mathompl/AquaLed/src/Nextion.ino

/*
   AQUALED Nextion support functions (c) T. Formanowski 2016-2017
   https://github.com/mathompl/AquaLed
 */



#include <Arduino.h>
#include <MemoryFree.h>
#include "Nextion.h"
#ifndef NO_NEXTION
// init nextion lcd
static void nexInit(void)
{
        NEXTION_BEGIN (9600);
        sendNextionEOL ();
        setPage(PAGE_HOME);
        setInt (NX_FIELD_BAUDS, NX_FIELD_EMPTY, (long)NEXTION_BAUD_RATE);
        NEXTION_FLUSH ();
        delay (50);
        NEXTION_BEGIN ((long)NEXTION_BAUD_RATE);
        setInt (NX_FIELD_BKCMD, NX_FIELD_EMPTY, (long)0);
        setPage (PAGE_HOME);
        toggleButtons ();
        refreshPWMNames ();
        forceRefresh = true;
        NEXTION_FLUSH ();
}

static void refreshPWMNames ()
{
        // init names
        for (byte i = 0; i < PWMS; i++)
        {
                setText (PAGE_HOME, NX_FIELD_LD1+i, (char*)pgm_read_word(&(nx_pwm_names[i])));
                delay(1);
                setText (PAGE_PWM_LIST, NX_FIELD_BLD1+i, (char*)pgm_read_word(&(nx_pwm_names[i])));
                delay(1);
        }
}

// main touch listener
static void nxTouch()
{
        while (NEXTION_AVAIL ()> 0)
        {

                char c = NEXTION_READ ();
                if (c == NEX_RET_EVENT_TOUCH_HEAD)
                {
                        memset(__touch_buffer, 0, sizeof (__touch_buffer));
                        __touch_event = true;
                }
                if (__touch_event)
                {
                        __touch_buffer[__touch_buffer_ix] = c;
                        __touch_buffer_ix++;
                }

                if (__touch_buffer_ix == 7)
                {
                        if (memcmp( __touch_buffer+3, nextionEol, 3)) handlePage ( __touch_buffer[1], __touch_buffer[2]);
                        __touch_buffer_ix = 0;
                        __touch_event = false;
                        return;
                }

        }
}
static void handlePage (byte pid, byte cid)
{
        lastTouch = currentMillis;
        switch (pid)
        {
        case PAGE_HOME:
                handleHomePage (cid);
                break;

        case PAGE_CONFIG:
                handleConfigPage (cid);
                break;

        case PAGE_SETTIME:
                handleSetTimePage (cid);
                break;

        case PAGE_SETTINGS:
                handleSettingsPage (cid);
                break;

        case PAGE_PWM:
                handlePWMPage (cid);
                break;

        case PAGE_TEST:
                handleTestPage (cid);
                break;

        case PAGE_SCREENSAVER:
                handleScreenSaver (cid);
                break;

        case PAGE_THERMO:
                handleThermoPage (cid);
                break;

        case PAGE_SCHEDULE:
                handleSchedulePage (cid);
                break;

        case PAGE_PWM_LIST:
                handlePWMListPage (cid);
                break;

        case PAGE_ERROR:
                handleScreenSaver (cid);
                break;

        case PAGE_PWMSTATUS:
                handlePWMStatus (cid);
                break;

        default:
                break;
        }
        lastTouch = currentMillis;
}

static void handleScreenSaver (byte cid)
{
        forceRefresh = true;
        setPage (PAGE_HOME);
        lastTouch = currentMillis;
        toggleButtons();
        refreshPWMNames ();
        refreshHomePage ();
}

static boolean setThermo (byte page, byte field, byte i)
{
        if (!getNumber(page, field, &t)) return false;
        for (byte k = 0; k < 8; k++)
                settings.sensors[i][k] = sensorsList[t].address[k];
        return true;
}

static void handleThermoPage (byte cid)
{
        boolean status = false;
        switch (cid)
        {
        // save
        case THERMOPAGE_BUTTON_SAVE:
                setPage (PAGE_SAVING);
                if (!setThermo (PAGE_THERMO, NX_FIELD_N0, LED_TEMPERATURE_FAN)) break;
                if (!setThermo (PAGE_THERMO, NX_FIELD_N1, SUMP_TEMPERATURE_FAN)) break;
                if (!setThermo (PAGE_THERMO, NX_FIELD_N2, WATER_TEMPERATURE_FAN)) break;
                writeEEPROMSettings ();
                lastTouch = currentMillis;
                setPage (PAGE_CONFIG);
                status = true;
                break;

        //cancel
        case THERMOPAGE_BUTTON_CANCEL:
                lastTouch = currentMillis;
                setPage (PAGE_CONFIG);
                status = true;
                break;

        default:
                break;
        }
        if (!status) setPage (PAGE_THERMO);
}

static void handleSchedulePage (byte cid)
{
        switch (cid)
        {
        //cancel
        case SCHEDULEPAGE_BUTTON_CLOSE:
                lastTouch = currentMillis;
                setPage (PAGE_CONFIG);
                break;

        default:
                break;
        }
}

static boolean handleTestSlider (int field, byte i)
{
        if (!getNumber(field, &t)) return false;
        pwmRuntime[i].valueCurrent = mapRound ((long)t, 0, 100, 0, PWM_I2C_MAX);
        pwmRuntime[i].testMode = true;
        return true;
}

static void handleTestPage (byte cid)
{
        switch (cid)
        {
        // pwms
        case TESTPAGE_SLIDER_PWM_1:
                handleTestSlider (NX_FIELD_N0, 0);
                break;
        case TESTPAGE_SLIDER_PWM_2:
                handleTestSlider (NX_FIELD_N1, 1);
                break;
        case TESTPAGE_SLIDER_PWM_3:
                handleTestSlider (NX_FIELD_N2, 2);
                break;
        case TESTPAGE_SLIDER_PWM_4:
                handleTestSlider (NX_FIELD_N3, 3);
                break;
        case TESTPAGE_SLIDER_PWM_5:
                handleTestSlider (NX_FIELD_N4, 4);
                break;
        case TESTPAGE_SLIDER_PWM_6:
                handleTestSlider (NX_FIELD_N5, 5);
                break;
        case TESTPAGE_SLIDER_PWM_7:
                handleTestSlider (NX_FIELD_N6, 6);
                break;
        case TESTPAGE_SLIDER_PWM_8:
                handleTestSlider (NX_FIELD_N7, 7);
                break;

        // close
        case TESTPAGE_BUTTON_CLOSE:
                lastTouch = currentMillis;
                forcePWMRecovery (true);
                for (byte i = 0; i < PWMS; i++)
                {
                        //pwmRuntime[i].valueTest = 0;
                        pwmRuntime[i].testMode = false;
                }
                setPage (PAGE_CONFIG);
                break;

        default:
                break;
        }
}

static void handlePWMPage (byte cid)
{
        int i;
        byte lastPin;
        byte lastI2C;
        boolean status = false;
        switch (cid)
        {
        // save
        case PWMPAGE_BUTTON_SAVE:
                setPage (PAGE_SAVING);
                if (!getNumber(PAGE_PWM, NX_FIELD_N9, &i)) break;
                if (i < 1 || i > PWMS) break;
                lastPin = pwmSettings[i - 1].pin;
                lastI2C = pwmSettings[i - 1].isI2C;

                if (!getNumber(PAGE_PWM, NX_FIELD_C0, &pwmSettings[i - 1].enabled )) break;
                if (!getNumber(PAGE_PWM, NX_FIELD_C1, &pwmSettings[i - 1].isNightLight)) break;
                if (!getNumber(PAGE_PWM, NX_FIELD_C2, &pwmSettings[i - 1].isProg)) break;
                if (!getNumber(PAGE_PWM, NX_FIELD_N0, &pwmSettings[i - 1].onHour)) break;
                if (!getNumber(PAGE_PWM, NX_FIELD_N1, &pwmSettings[i - 1].onMinute)) break;
                if (!getNumber(PAGE_PWM, NX_FIELD_N2, &pwmSettings[i - 1].offHour)) break;
                if (!getNumber(PAGE_PWM, NX_FIELD_N3, &pwmSettings[i - 1].offMinute)) break;
                if (!getNumber(PAGE_PWM, NX_FIELD_N4, &pwmSettings[i - 1].sunriseLenght)) break;
                if (!getNumber(PAGE_PWM, NX_FIELD_N5, &pwmSettings[i - 1].sunsetLenght)) break;
                if (!getNumber(PAGE_PWM, NX_FIELD_N6, &pwmSettings[i - 1].valueNight)) break;
                if (!getNumber(PAGE_PWM, NX_FIELD_N7, &pwmSettings[i - 1].valueDay)) break;
                if (!getNumber(PAGE_PWM, NX_FIELD_N8, &pwmSettings[i - 1].valueProg)) return;
                if (!getNumber(PAGE_PWM, NX_FIELD_N10, &pwmSettings[i - 1].pin)) break;
                if (!getNumber(PAGE_PWM, NX_FIELD_N11, &pwmSettings[i - 1].watts)) break;
                if (!getNumber(PAGE_PWM, NX_FIELD_C3, &pwmSettings[i - 1].isI2C)) break;
                if (!getNumber(PAGE_PWM, NX_FIELD_C4, &pwmSettings[i - 1].invertPwm)) break;
                if (!getNumber(PAGE_PWM, NX_FIELD_C5, &pwmSettings[i - 1].useLunarPhase)) break;

                if (lastPin != pwmSettings[i - 1].pin || lastI2C != pwmSettings[i - 1].isI2C) initPWM ( i-1 );

                //pwmSettings[i - 1].valueNight = mapRound ((byte)pwmSettings[i - 1].valueNight, 0, 255, 0, PWM_I2C_MAX);
                pwmSettings[i - 1].valueProg = mapRound (pwmSettings[i - 1].valueProg, 0, 100, 0, PWM_I2C_MAX);
                pwmSettings[i - 1].valueDay = mapRound (pwmSettings[i - 1].valueDay, 0, 100, 0, PWM_I2C_MAX);
                lastTouch = currentMillis;
                writeEEPROMPWMConfig (i - 1);
                updateChannelTimes (i-1);
                setPage (PAGE_PWM_LIST);
                status = true;
                break;

        //  cancel
        case PWMPAGE_BUTTON_CANCEL:
                lastTouch = currentMillis;
                setPage (PAGE_PWM_LIST);
                status = true;
                break;

        default:
                status = true;
                break;
        }
        if (!status) setPage (PAGE_PWM_LIST);
}

static void handleSettingsPage (byte cid)
{
        boolean status = false;
        switch (cid)
        {
        // save
        case SETTINGSPAGE_BUTTON_SAVE:
                setPage (PAGE_SAVING);
                if (!getNumber(PAGE_SETTINGS,NX_FIELD_N0, &settings.maxTemperatures[LED_TEMPERATURE_FAN] )) break;
                if (!getNumber(PAGE_SETTINGS,NX_FIELD_N1, &settings.maxTemperatures[SUMP_TEMPERATURE_FAN])) break;
                if (!getNumber(PAGE_SETTINGS,NX_FIELD_N2, &settings.maxTemperatures[WATER_TEMPERATURE_FAN])) break;
                if (!getNumber(PAGE_SETTINGS,NX_FIELD_N3, &settings.pwmDimmingTime)) break;
                if (!getNumber(PAGE_SETTINGS,NX_FIELD_N4, &settings.screenSaverTime)) break;
                if (!getNumber(PAGE_SETTINGS,NX_FIELD_C0, &settings.softDimming)) break;
                writeEEPROMSettings ();
                lastTouch = currentMillis;
                setPage (PAGE_CONFIG);
                status = true;
                break;

        // cancel
        case SETTINGSPAGE_BUTTON_CANCEL:
                lastTouch = currentMillis;
                setPage (PAGE_CONFIG);
                status = true;
                break;

        default:
                break;
        }
        if (!status) setPage (PAGE_SETTINGS);
}

static void handleSetTimePage (byte cid)
{
        int setHour, setMinute, setYear, setMonth, setDay;
        boolean status = false;
        switch (cid)
        {
        // save
        case TIMEPAGE_BUTTON_SAVE:
                setPage (PAGE_SAVING);
                if (!getNumber(PAGE_SETTIME, NX_FIELD_N0, &setHour)) break;
                if (!getNumber(PAGE_SETTIME, NX_FIELD_N1, &setMinute)) break;
                if (!getNumber(PAGE_SETTIME, NX_FIELD_N2, &setDay)) break;
                if (!getNumber(PAGE_SETTIME, NX_FIELD_N3, &setMonth)) break;
                if (!getNumber(PAGE_SETTIME, NX_FIELD_N4, &setYear)) break;
                if (!getNumber(PAGE_SETTIME, NX_FIELD_C0, &settings.dst)) break;
                RTC.adjust(DateTime(setYear, setMonth, setDay, setHour, setMinute,0));
                readTimes ();
                adjustDST ();
                writeEEPROMSettings ();
                lastTouch = currentMillis;
                setPage (PAGE_CONFIG);
                lastTouch = currentMillis;
                forcePWMRecovery (false);
                status = true;
                break;

        // cancel
        case TIMEPAGE_BUTTON_CANCEL:
                lastTouch = currentMillis;
                setPage (PAGE_CONFIG);
                lastTouch = currentMillis;
                status = true;
                break;

        default:
                status = true;
                break;
        }
        if (!status) setPage (PAGE_SETTIME);
}

static void drawSchedule ()
{
        int startL;
        int min_start;
        int min_stop;
        int stopL;
        int stopM;
        int min_sunrise;
        int min_sunrise_left;
        int min_sunset;
        int min_sunset_left;
        boolean midnight = false;

        for (byte i = 0; i < PWMS; i++)
        {
                min_start = (int)pwmSettings[i].onHour * (int)60 + (int)pwmSettings[i].onMinute;
                min_stop = (int)pwmSettings[i].offHour * (int)60 + (int)pwmSettings[i].offMinute;

                // background
                if (pwmSettings[i].isNightLight == 1)
                        fillRect (offset * i + startx, starty, width, height, COLOR_DARKBLUE);
                else
                        fillRect (offset * i + startx, starty, width, height, COLOR_RED);

                // off
                if (pwmSettings[i].enabled == 0) continue;

                // light
                if (min_stop < min_start) midnight = true;
                else midnight = false;

                if (!midnight)
                {
                        startL = map (min_start, 0, min_hour, starty, starty + height);
                        stopL = map (min_stop, 0, min_hour, starty, starty + height ) - startL;
                        fillRect (offset * i + startx, startL, width, stopL, COLOR_GREEN);
                }
                else
                {
                        startL = map (min_start, 0, min_hour, starty, starty + height);
                        stopL = map (min_stop, 0, min_hour, starty, starty + height ) - 30;
                        stopM =  map (min_hour, 0, min_hour, starty, starty + height ) - startL;
                        // start to midnight
                        fillRect (offset * i + startx, startL, width, stopM, COLOR_GREEN);
                        // midnight to end
                        fillRect (offset * i + startx, starty, width, stopL, COLOR_GREEN);
                }
                // sunrise
                min_sunrise  = min_start + (int)pwmSettings[i].sunriseLenght;
                if (min_sunrise > min_hour) midnight = true; else midnight = false;

                if (!midnight)
                {
                        startL = map (min_start, 0, min_hour, starty, starty + height);
                        stopL = map (min_sunrise, 0, min_hour, starty, starty + height ) - startL;
                        fillRect (offset * i + startx, startL, width, stopL, COLOR_BLUE);
                }
                else
                {
                        startL = map (min_start, 0, min_hour, starty, starty + height);
                        stopM =  map (min_hour, 0, min_hour, starty, starty + height ) - startL;
                        min_sunrise_left = min_sunrise - min_hour;
                        stopL = map (min_sunrise_left, 0, min_hour, starty, starty + height ) - starty;
                        // start to midnight
                        fillRect (offset * i + startx, startL, width, stopM, COLOR_BLUE);
                        // midnight to end
                        fillRect (offset * i + startx, starty, width, stopL, COLOR_BLUE);
                }
                // sunset
                min_sunset  = min_stop - (int)pwmSettings[i].sunsetLenght;
                if (min_sunset < 0) midnight = true; else midnight = false;
                if (!midnight)
                {
                        startL = map (min_sunset, 0, min_hour, starty, starty + height);
                        stopL = map (min_stop, 0, min_hour, starty, starty + height ) - startL;
                        fillRect (offset * i + startx, startL, width, stopL, COLOR_BLUE);
                }
                else
                {
                        min_sunset_left = min_hour + min_sunset;
                        stopL  = map (min_stop, 0, min_hour, starty, starty + height ) - starty;
                        startL = map (min_sunset_left, 0, min_hour, starty, starty + height);
                        stopM =  map (min_hour, 0, min_hour, starty, starty + height ) - startL;
                        // zero to end
                        fillRect (offset * i + startx, starty, width, stopL, COLOR_BLUE);
                        // rest till midnight
                        fillRect (offset * i + startx, startL, width, stopM, COLOR_BLUE);
                }
        }
        int min_now = map (currHour * 60 + currMinute, 0, min_hour, starty, starty + height);
        fillRect (hour_startx, min_now, hour_stopx, 1, COLOR_YELLOW);
        // siatka dodatkowa
        /*
           for (int i = 0 ; i < 24; i++)
           {
           fillRect (40, 10 * i + starty+1, 180, 1, COLOR_DARKGRAY);

           }*/
}

static void handleConfigPage (byte cid)
{
        byte s;
        byte idxLed, idxSump, idxWater;

        char tempbuff[150] = {0};
        switch (cid)
        {
        // schedule
        case CONFIGPAGE_BUTTON_SCHEDULE:
                setPage (PAGE_SCHEDULE);
                drawSchedule ();
                break;

        // close
        case CONFIGPAGE_BUTTON_CLOSE:
                forceRefresh = true;
                setPage (PAGE_HOME);
                toggleButtons();
                refreshHomePage ();
                break;

        // thermo setup
        case CONFIGPAGE_BUTTON_THERMO:
              #ifndef NO_TEMPERATURE
                setPage (PAGE_THERMO);
                s = discoverOneWireDevices ();
                memset (tempbuff, 0, sizeof (tempbuff));
                setValue (NX_FIELD_VA0, (s-1));
                for (byte i = 0; i < s; i++)
                {
                        sprintf(tempbuff + strlen (tempbuff), "%d. ", i);
                        if (i == 0)
                        {
                                strcpy (tempbuff + strlen (tempbuff), "BRAK ");
                        }
                        else
                        {
                                if (sensorsList[i].detected)
                                        strcpy (tempbuff + strlen (tempbuff), "* ");
                                for (byte k = 0; k < 8; k++)
                                        sprintf (tempbuff + strlen (tempbuff), "%02x ", sensorsList[i].address[k]);
                        }
                        strcpy  (tempbuff + strlen (tempbuff), "\r\n");
                }
                idxLed = listContains (settings.sensors[LED_TEMPERATURE_FAN]);
                idxSump = listContains (settings.sensors[SUMP_TEMPERATURE_FAN]);
                idxWater = listContains (settings.sensors[WATER_TEMPERATURE_FAN]);
                if (idxLed == 255) idxLed = 0;
                if (idxSump == 255) idxSump = 0;
                if (idxWater == 255) idxWater = 0;
                setValue (NX_FIELD_N0, idxLed);
                setValue (NX_FIELD_N1, idxSump);
                setValue (NX_FIELD_N2, idxWater);
                setText (NX_FIELD_T4, (String) tempbuff);
              #endif
                break;

        // test
        case CONFIGPAGE_BUTTON_TEST:
                setPage (PAGE_TEST);
                for (byte i = 0; i < PWMS; i++)
                {
                        setValue (NX_FIELD_N0+i, mapRound (pwmRuntime[i].valueCurrent, 0, PWM_I2C_MAX, 0, 100));
                        setValue (NX_FIELD_C1+i, mapRound (pwmRuntime[i].valueCurrent, 0, PWM_I2C_MAX, 0, 100));
                        //pwmRuntime[i].valueTest = pwmRuntime[i].valueCurrent;
                        pwmRuntime[i].testMode = false;
                }
                break;

        // hour and date setup
        case CONFIGPAGE_BUTTON_TIME:
                setPage (PAGE_SETTIME);
                setValue (NX_FIELD_N0, RTC.now().hour ());
                setValue (NX_FIELD_N1, RTC.now().minute ());
                setValue (NX_FIELD_N2, RTC.now().day ());
                setValue (NX_FIELD_N3, RTC.now().month ());
                setValue (NX_FIELD_N4, RTC.now().year());
                setValue (NX_FIELD_C0, settings.dst);
                break;

        // other settings
        case CONFIGPAGE_BUTTON_SETTINGS:
                setPage (PAGE_SETTINGS);
                setValue (NX_FIELD_N0, settings.maxTemperatures[LED_TEMPERATURE_FAN]);
                setValue (NX_FIELD_N1, settings.maxTemperatures[SUMP_TEMPERATURE_FAN]);
                setValue (NX_FIELD_N2, settings.maxTemperatures[WATER_TEMPERATURE_FAN]);
                setValue (NX_FIELD_N3, settings.pwmDimmingTime);
                setValue (NX_FIELD_N4, settings.screenSaverTime);
                setValue (NX_FIELD_C0, settings.softDimming);
                break;

        // pwm config
        case CONFIGPAGE_BUTTON_PWM:
                setPage (PAGE_PWM_LIST);
                break;

        default:
                break;
        }
}


static void handlePWMStatus (byte cid)
{

        switch (cid)
        {
        // cancel
        case PWMSTATUSPAGE_BUTTON_CLOSE:
                lastTouch = currentMillis;
                setPage (PAGE_HOME);
                toggleButtons();
                refreshHomePage ();
                lastTouch = currentMillis;
                break;

        default:
                break;
        }
}

static void handlePWMListPage (byte cid)
{
        byte tmin, tmax, tamb;

        switch (cid)
        {
        // enter pwm settings
        case PWMCONFIGPAGE_BUTTON_PWM_1:
        case PWMCONFIGPAGE_BUTTON_PWM_2:
        case PWMCONFIGPAGE_BUTTON_PWM_3:
        case PWMCONFIGPAGE_BUTTON_PWM_4:
        case PWMCONFIGPAGE_BUTTON_PWM_5:
        case PWMCONFIGPAGE_BUTTON_PWM_6:
        case PWMCONFIGPAGE_BUTTON_PWM_7:
        case PWMCONFIGPAGE_BUTTON_PWM_8:
                tmin = pwmSettings[cid - 1].valueNight;
                tmax = (byte) mapRound (pwmSettings[cid - 1].valueDay, 0, PWM_I2C_MAX, 0, 100);
                tamb = (byte) mapRound (pwmSettings[cid - 1].valueProg, 0, PWM_I2C_MAX, 0, 100);
                setPage (PAGE_PWM);
                setValue (NX_FIELD_C0, pwmSettings[cid - 1].enabled);
                setValue (NX_FIELD_C1, pwmSettings[cid - 1].isNightLight);
                setValue (NX_FIELD_C2, pwmSettings[cid - 1].isProg);
                setValue (NX_FIELD_N0, pwmSettings[cid - 1].onHour);
                setValue (NX_FIELD_N1, pwmSettings[cid - 1].onMinute);
                setValue (NX_FIELD_N2, pwmSettings[cid - 1].offHour);
                setValue (NX_FIELD_N3, pwmSettings[cid - 1].offMinute);
                setValue (NX_FIELD_N4, pwmSettings[cid - 1].sunriseLenght);
                setValue (NX_FIELD_N5, pwmSettings[cid - 1].sunsetLenght);
                setValue (NX_FIELD_N6, tmin);
                setValue (NX_FIELD_N7, tmax);
                setValue (NX_FIELD_N8, tamb);
                setValue (NX_FIELD_N9, cid);
                setValue (NX_FIELD_N10, pwmSettings[cid - 1].pin);
                setValue (NX_FIELD_N11, pwmSettings[cid - 1].watts);
                setValue (NX_FIELD_C3, pwmSettings[cid - 1].isI2C);
                setValue (NX_FIELD_C4, pwmSettings[cid - 1].invertPwm);
                setValue (NX_FIELD_C5, pwmSettings[cid - 1].useLunarPhase);
                setText (NX_FIELD_T4,  (char*)pgm_read_word(&(nx_pwm_names[cid -1])));
                break;

        // cancel
        case PWMCONFIGPAGE_BUTTON_CLOSE:
                lastTouch = currentMillis;
                setPage (PAGE_CONFIG);
                lastTouch = currentMillis;
                break;

        default:
                break;
        }
}

static void handleHomePage (byte cid)
{

        switch (cid)
        {

        // config show
        case HOMEPAGE_BUTTON_CONFIG:
                setPage (PAGE_CONFIG);
                break;

        //toggle night mode
        case HOMEPAGE_BUTTON_NIGHT:
                if (settings.forceAmbient  == 1 || settings.forceOFF  == 1) return;
                if (settings.forceNight == 1)
                {
                        settings.forceNight = 0;
                        forcePWMRecovery (false);
                }
                else
                {
                        settings.forceNight = 1;
                        forceDimmingRestart ();
                }

                toggleButtons();
                writeEEPROMForceNight ();
                break;

        // ambient toggle
        case HOMEPAGE_BUTTON_AMBIENT:
                if (settings.forceOFF == 1 || settings.forceNight == 1) return;
                if (settings.forceAmbient == 1)
                {
                        settings.forceAmbient = 0;
                        forcePWMRecovery (false);
                }
                else
                {
                        settings.forceAmbient = 1;
                        forceDimmingRestart ();
                }

                toggleButtons();
                writeEEPROMForceAmbient ();
                break;

        // off/on toggle
        case HOMEPAGE_BUTTON_OFF:
                if (settings.forceOFF == 1)
                {
                        settings.forceOFF = 0;
                        forcePWMRecovery (false);
                }
                else
                {
                        settings.forceOFF = 1;
                        forceDimmingRestart ();
                }
                toggleButtons();
                writeEEPROMForceOff ();
                break;

        // fans toggle
        case HOMEPAGE_BUTTON_FAN_WATER:
                sensors[WATER_TEMPERATURE_FAN].fanStatus = !sensors[WATER_TEMPERATURE_FAN].fanStatus;
                relaySwitch (WATER_TEMPERATURE_FAN);
                refreshHomePage ();
                break;

        case HOMEPAGE_BUTTON_FAN_LAMP:
                sensors[LED_TEMPERATURE_FAN].fanStatus = !sensors[LED_TEMPERATURE_FAN].fanStatus;
                relaySwitch (LED_TEMPERATURE_FAN);
                refreshHomePage ();
                break;

        case HOMEPAGE_BUTTON_FAN_SUMP:
                sensors[SUMP_TEMPERATURE_FAN].fanStatus = !sensors[SUMP_TEMPERATURE_FAN].fanStatus;
                relaySwitch (SUMP_TEMPERATURE_FAN);
                refreshHomePage ();
                break;

        case HOMEPAGE_PWMSTATUS1:
        case HOMEPAGE_PWMSTATUS2:
        case HOMEPAGE_PWMSTATUS3:
        case HOMEPAGE_PWMSTATUS4:
        case HOMEPAGE_PWMSTATUS5:
        case HOMEPAGE_PWMSTATUS6:
        case HOMEPAGE_PWMSTATUS7:
        case HOMEPAGE_PWMSTATUS8:
                activePwmStatus = cid - HOMEPAGE_PWMSTATUS1;
                setPage (PAGE_PWMSTATUS);
                updatePWMStatusPage (activePwmStatus);
                break;

        default:
                break;
        }
}

static void toggleButton (byte value, byte field, byte pic_on, byte pic_off)
{
        if (value == 1) setInt(field,NX_CMD_PIC, pic_on); else setInt(field,NX_CMD_PIC,  pic_off);
}

// toggle home page buttons images
static void toggleButtons()
{
        toggleButton (settings.forceOFF, NX_FIELD_BO, NX_PIC_BO_ON, NX_PIC_BO_OFF);
        toggleButton (settings.forceAmbient, NX_FIELD_BA, NX_PIC_BA_ON, NX_PIC_BA_OFF);
        toggleButton (settings.forceNight, NX_FIELD_BN, NX_PIC_BN_ON, NX_PIC_BN_OFF);
}

#ifndef NO_TEMPERATURE
void updateTempField (byte field, byte sensor, byte max, byte min)
{
        if (sensors[sensor].nxTemperature != sensors[sensor].temperature  || forceRefresh)
        {
                if (sensors[sensor].temperature != TEMP_ERROR)
                {
                        setTextFloat(field, sensors[sensor].temperature,1,NX_STR_DEGREE);
                        sensors[sensor].nxTemperature = sensors[sensor].temperature;
                        if (sensors[sensor].temperature < min || sensors[sensor].temperature > max)
                                setInt (field, NX_CMD_PCO, COLOR_LIGHTRED);
                        else
                                setInt (field, NX_CMD_PCO,  COLOR_LIGHTGREEN);
                }
                else
                {
                        sensors[sensor].nxTemperature = TEMP_ERROR;
                        setText(field, NX_STR_DASH);
                }
        }
}

void updateFanField (byte field, byte sensor)
{
        if (sensors[sensor].nxFanStatus == sensors[sensor].fanStatus) return;
        if (!sensors[sensor].fanStatus) setText (field, NX_STR_EMPTY);
        else setText (field, NX_STR_FAN);
        sensors[sensor].nxFanStatus = sensors[sensor].fanStatus;
}
#endif

static void updateWaterTemp()
{
    #ifndef NO_TEMPERATURE
        updateTempField (NX_FIELD_WT, WATER_TEMPERATURE_FAN,settings.maxTemperatures[WATER_TEMPERATURE_FAN], WATER_TEMPERATURE_MIN);
    #endif
}


static void updatePWMStatusPage (byte i)
{
        uint16_t color;
        byte icon;
        setText (NX_FIELD_EMPTY, NX_FIELD_T0, (char*)pgm_read_word(&(nx_pwm_names[i])));
        getColorAndIcon (i, &color, &icon);
        setTextFloat (NX_FIELD_T1,  getPercent (i), 1, NX_STR_PERCENT);
        setTextInt (NX_FIELD_T2, pwmRuntime[i].valueCurrent);
        setText (NX_FIELD_T3, icon);
        setInt (NX_FIELD_T3, NX_CMD_PCO,  color);
        setTextInt (NX_FIELD_T4, pwmRuntime[i].secondsLeft);
        setTextInt (NX_FIELD_T5, pwmRuntime[i].valueGoal);
        setTextFloat (NX_FIELD_T6, pwmRuntime[i].watts, 1, NX_STR_WATTS);
        setTextFloat (NX_FIELD_T7, pwmRuntime[i].step,3, NX_FIELD_EMPTY);
        setTextFloat (NX_FIELD_T9, moonPhases[moonPhase],0,NX_STR_PERCENT);
        uint32_t uptime  = RTC.now ().unixtime() - startTimestamp;
        char buf[12];
        memset (buf, 0, sizeof (buf));
        long mins=uptime/60;
        long hours=mins/60;
        long days=hours/24;
        mins=mins-(hours*60);
        hours=hours-(days*24);
        sprintf (buf, "%lud %02lu:%02lu",days, hours,mins);
        setText (NX_FIELD_T8, String (buf));
}


static void updateHomePage()
{
        #ifndef NO_TEMPERATURE
        updateWaterTemp();
        updateTempField (NX_FIELD_LT, LED_TEMPERATURE_FAN,settings.maxTemperatures[LED_TEMPERATURE_FAN], 0);
        updateTempField (NX_FIELD_ST, SUMP_TEMPERATURE_FAN,settings.maxTemperatures[SUMP_TEMPERATURE_FAN], 0);
        #endif
        for (byte i = 0; i < PWMS; i++)
        {
                byte valueField = 66+i;
                byte iconField =  3+i;
                if (!pwmRuntime[i].valueCurrent && pwmSettings[i].enabled == 0 && (pwmRuntime[i].nxPwmLast != 0 || forceRefresh))
                {
                        setText (valueField, NX_STR_DASH);
                        setText (iconField, NX_STR_SPACE);
                        pwmRuntime[i].nxPwmLast = 0;
                        continue;
                }

                if (pwmRuntime[i].nxPwmLast!=pwmRuntime[i].valueCurrent || forceRefresh)
                {
                        uint16_t color;
                        byte icon;
                        getColorAndIcon (i, &color, &icon);
                        pwmRuntime[i].nxPwmLast = pwmRuntime[i].valueCurrent;
                        setTextFloat (valueField,  getPercent (i), 1, NX_STR_PERCENT);
                        setText (iconField, icon);
                        setInt (iconField, NX_CMD_PCO,  color);
                }
        }
        #ifndef NO_TEMPERATURE
        updateFanField (NX_FIELD_T0, WATER_TEMPERATURE_FAN);
        updateFanField (NX_FIELD_T1, LED_TEMPERATURE_FAN);
        updateFanField (NX_FIELD_T2, SUMP_TEMPERATURE_FAN);
        #endif
}

static double getPercent (byte i)
{
        return mapDouble((double)pwmRuntime[i].valueCurrent, 0.0, (double)PWM_I2C_MAX, 0.0, 100.0);
}

static void getColorAndIcon (byte i, uint16_t *color, byte *icon)
{
        *color = COLOR_WHITE;
        *icon = NX_STR_SPACE;
        if (pwmRuntime[i].isSunrise )
        {
                *icon = NX_STR_SUNRISE;
                *color = COLOR_LIGHTYELLOW;
        }
        else if (pwmRuntime[i].isSunset )
        {
                *icon = NX_STR_SUNSET;
                *color = COLOR_ORANGE;
        }
        else if (pwmRuntime[i].recoverLastState)
        {
                *icon = NX_STR_RECOVER;
                *color = COLOR_LIGHTGREEN;
        }
        else if (pwmRuntime[i].valueCurrent < pwmRuntime[i].valueGoal)
        {
                *icon = NX_STR_UP;

        }
        else if (pwmRuntime[i].valueCurrent > pwmRuntime[i].valueGoal) *icon = NX_STR_DOWN;
        else if (pwmRuntime[i].valueCurrent == 0 || pwmSettings[i].enabled == 0)
        {
                *icon = NX_STR_OFF;
                *color = COLOR_LIGHTRED;
        }
        else if (pwmRuntime[i].isNight)
        {
                if (pwmSettings[i].useLunarPhase)
                {
                        *color = rgb565 (map (moonPhases[moonPhase], 0,100,150,255));
                }
                *icon = NX_STR_NIGHT;
        }
        else if (pwmRuntime[i].valueCurrent == pwmSettings[i].valueDay)
        {
                *icon = NX_STR_ON;
                *color = COLOR_YELLOW;
        }
}

static uint16_t rgb565( byte rgb)
{
        uint16_t ret  = (rgb & 0xF8) << 8;// 5 bits
        ret |= (rgb & 0xFC) << 3;       // 6 bits
        ret |= (rgb & 0xF8) >> 3;       // 5 bits
        return( ret);
}

static void displayWats ()
{
        if(watts!=lastWatts || forceRefresh) setTextFloat (NX_FIELD_WA, watts, 1, NX_STR_WATTS);
        lastWatts= watts;
}

static void timeDisplay()
{
        char buff[7] = {0};
        memset(buff, 0, sizeof (buff));
        if (time_separator % 2 == 0)
                sprintf(buff + strlen(buff), "%02u:%02u", currHour, currMinute);
        else sprintf(buff + strlen(buff), "%02u %02u", currHour, currMinute);
        setText (NX_FIELD_H, (String)buff);
        time_separator++;
}

static void refreshHomePage ()
{
        timeDisplay();
        updateHomePage();
        displayWats ();

}

/*static void displayMemory ()
   {
        double freemem = ( (double) getFreeMemory() / (double) 2048) *100;
        setTextFloat (NX_FIELD_DEBUG2, freemem,  1, NX_STR_PERCENT);
   }*/
/*
   static void nxSetDebug ()
   {
    if (nxScreen == PAGE_SCREENSAVER )
    {
        setTextInt (NX_FIELD_DEBUG1, codePoint);

    }
   }
 */

static void nxDisplay ()
{
        if (currentMillis - previousNxInfo > NX_INFO_RESOLUTION)
        {
                previousNxInfo = currentMillis;
                if (lampOverheating)
                {
                        nxScreen = PAGE_ERROR;
                        setPage (PAGE_ERROR);
                        setText (NX_FIELD_T1, (char*)pgm_read_word(&(nx_errors[0])) );
                }
                if (max_watts_exceeded)
                {
                        nxScreen = PAGE_ERROR;
                        setPage (PAGE_ERROR);
                        setText (NX_FIELD_T1, (char*)pgm_read_word(&(nx_errors[1])) );
                }
                if (nxScreen == PAGE_SCREENSAVER )
                {
                        timeDisplay();
                        updateWaterTemp();
                        displayWats ();
                        //  displayMemory ();
                        forceRefresh = false;
                }
                if (nxScreen == PAGE_HOME )
                {
                        if (forceRefresh) refreshPWMNames ();
                        refreshHomePage ();
                        forceRefresh = false;
                }
                if (nxScreen == PAGE_PWMSTATUS)
                {
                        updatePWMStatusPage(activePwmStatus);
                }
                // screensaver
                if (currentMillis - lastTouch > settings.screenSaverTime*1000 && nxScreen != PAGE_SCREENSAVER && settings.screenSaverTime > 0
                    && nxScreen != PAGE_TEST
                    && nxScreen != PAGE_SETTINGS
                    && nxScreen != PAGE_PWM
                    && nxScreen != PAGE_SETTIME
                    && nxScreen != PAGE_THERMO
                    && nxScreen != PAGE_SCHEDULE
                    && nxScreen != PAGE_PWM_LIST
                    && nxScreen != PAGE_ERROR
                    && nxScreen != PAGE_SAVING
                    && nxScreen != PAGE_PWMSTATUS
                    )
                {
                        setPage (PAGE_SCREENSAVER);
                        setText (NX_FIELD_T1,NX_STR_EMPTY);
                        forceRefresh = true;
                }
        }
        if (lastTouch == 0) lastTouch = currentMillis;

}

/* NEXTION COMMUNICATION */

static void sendNextionEOL ()
{
        NEXTION_WRITEB(nextionEol, 3);
}

static void startCommand  (byte page, byte field, byte command, boolean eq, boolean pth)
{
        if (page!=NX_FIELD_EMPTY)
        {
                printPGM( (char*)pgm_read_word(&(nx_pages[page])));
                printPGM( (char*)pgm_read_word(&(nx_commands[NX_CMD_DOT])));
        }
        if (field!=NX_FIELD_EMPTY) printPGM( (char*)pgm_read_word(&(nx_fields[field])));
        if (command!=NX_CMD_EMPTY) printPGM( (char*)pgm_read_word(&(nx_commands[command])));
        if (eq) printPGM( (char*)pgm_read_word(&(nx_commands[NX_CMD_EQ])));
        else printPGM( (char*)pgm_read_word(&(nx_commands[NX_CMD_SPACE])));
        if (pth) printPGM( (char*)pgm_read_word(&(nx_commands[NX_CMD_PARENTH])));
}

static void endCommand  (boolean pth)
{
        if (pth) printPGM( (char*)pgm_read_word(&(nx_commands[NX_CMD_PARENTH])));
        sendNextionEOL ();
}

static void setInt (byte field, long cmd, long val)
{
        startCommand (NX_FIELD_EMPTY, field, cmd,  true, false);
        NEXTION_PRINT(val);
        endCommand (false);
}


static void setTextFloat (byte field, double txt, byte prec, byte str)
{
        startCommand (NX_FIELD_EMPTY, field, NX_CMD_TXT, true,  true);
        NEXTION_PRINTF( txt, prec );
        if (str!=NX_FIELD_EMPTY) printPGM( (char*)pgm_read_word(&(nx_strings[str])));
        endCommand (true);
}
static void setValue (byte field, unsigned int val)
{
        startCommand (NX_FIELD_EMPTY, field, NX_CMD_VAL,  true, false);
        NEXTION_PRINT(val);
        endCommand (false);
}

static void setTextInt (byte field, int txt)
{
        startCommand (NX_FIELD_EMPTY, field, NX_CMD_TXT, true,  true);
        NEXTION_PRINT( txt );
        endCommand (true);
}

static void setPage (byte number)
{
        startCommand (NX_FIELD_EMPTY, NX_FIELD_EMPTY, NX_CMD_PAGE, false, false);
        NEXTION_PRINT(number);
        endCommand (false);
        nxScreen = number;
}

static void setText (byte field, int nx_string_id)
{
        setText (field, (char*)pgm_read_word(&(nx_strings[nx_string_id])));
}

static void setText (byte field, String text)
{
        startCommand (NX_FIELD_EMPTY, field, NX_CMD_TXT,  true, true);
        //NEXTION_PRINT(text);
        writeString (text);
        endCommand (true);
}

static void setText (byte page, byte field, const char * text)
{
        startCommand (page, field, NX_CMD_TXT, true,  true);
        printPGM(text);
        endCommand (true);
}

static void setText (byte field, const char * text)
{
        setText (NX_FIELD_EMPTY, field, text);
}

static bool getNumber (byte field, int *result)
{
        return getNumber (255,  field, result);
}

static bool getNumber (byte page, byte field, byte *result)
{
        int t;
        if (getNumber (page, field, &t))
        {
                *result = (byte) t;
                return true;
        }
        return false;
}

static bool getNumber (byte page, byte field, int *result)
{
        printPGM( (char*)pgm_read_word(&(nx_commands[NX_CMD_GET])));
        printPGM( (char*)pgm_read_word(&(nx_commands[NX_CMD_SPACE])));
        if (page!=255)
        {
                printPGM( (char*)pgm_read_word(&(nx_pages[page])));
                printPGM( (char*)pgm_read_word(&(nx_commands[NX_CMD_DOT])));
        }
        printPGM( (char*)pgm_read_word(&(nx_fields[field])));
        printPGM( (char*)pgm_read_word(&(nx_commands[NX_CMD_VAL])));
        sendNextionEOL ();
        uint8_t temp[8] = {0};
        uint32_t r;
        NEXTION_SETTIMEOUT(500);
        if (sizeof(temp) != NEXTION_READBYTES((char *)temp, sizeof(temp)))
        {
                return false;
        }
        if (temp[0] == NEX_RET_NUMBER_HEAD && memcmp( temp+5, nextionEol, 3) == 0)
        {
                r = ((uint32_t)temp[4] << 24) | ((uint32_t)temp[3] << 16) | ((uint32_t)temp[2] << 8) | ((uint32_t)temp[1]);
                *result = (int) r;
                return true;
        }
        return false;
}

// fills nextion rectangle
static void fillRect (int x, int y, int w, int h, int color)
{

        printPGM( (char*)pgm_read_word(&(nx_commands[NX_CMD_FILL])));
        printPGM( (char*)pgm_read_word(&(nx_commands[NX_CMD_SPACE])));
        NEXTION_PRINT (x);
        printPGM( (char*)pgm_read_word(&(nx_commands[NX_CMD_COMMA])));
        NEXTION_PRINT (y);
        printPGM( (char*)pgm_read_word(&(nx_commands[NX_CMD_COMMA])));
        NEXTION_PRINT (w);
        printPGM( (char*)pgm_read_word(&(nx_commands[NX_CMD_COMMA])));
        NEXTION_PRINT (h);
        printPGM( (char*)pgm_read_word(&(nx_commands[NX_CMD_COMMA])));
        NEXTION_PRINT (color);
        sendNextionEOL ();
}

static void printPGM (const char * str)
{
        if (!str) return;
        char c;
        while ((c = pgm_read_byte(str++)))
                NEXTION_WRITE (c);
}

void writeString(String stringData) { // Used to serially push out a String with Serial.write()
        for (byte i = 0; i < stringData.length(); i++)
        {
                NEXTION_WRITE (stringData[i]); // Push each char 1 by 1 on each loop pass
        }
}

#endif
